renr3/HIGROTERM/Source Code/A000_SourceCode_HIGROTERM_EnPtVersion_v0_4_DUE_Version/A80_Icons.ino

/* ICONS BITMAPS
    TODO 4: Separate this icons bitmaps into an external .c file. ### Implemented on v0.4
 *  */

// int[] img_home2_png = { //:Pxs
uint16_t img_home2_png[1024] PROGMEM = { //:Wiring
  0x02FF, 0x02FF, 0x02FF, 0x02FF, 0x02FF, 0x02FF, 0x02FF, 0x02FF, 0x02FF, 0x02FF, 0x02FF, 0x02FF, 0x02FF, 0xDF3F, 0xFFDF, 0xFFDF,
  0xFFDF, 0xFFDF, 0xDF5F, 0x02FF, 0x02FF, 0x02FF, 0x02FF, 0x02FF, 0x02FF, 0x02FF, 0x02FF, 0x02FF, 0x02FF, 0x02FF, 0x02FF, 0x02FF,
  0x02FF, 0x02FF, 0x02FF, 0x02FF, 0x02FF, 0x02FF, 0x02FF, 0x02FF, 0x02FF, 0x02FF, 0x02FF, 0x02FF, 0xF7BF, 0xFFDF, 0xFFDF, 0xFFDF,
  0xFFDF, 0xFFDF, 0xFFDF, 0xF7DF, 0x02FF, 0x02FF, 0x02FF, 0xC6DF, 0xFFDF, 0xFFDF, 0x239F, 0x02FF, 0x02FF, 0x02FF, 0x02FF, 0x02FF,
  0x02FF, 0x02FF, 0x02FF, 0x02FF, 0x02FF, 0x02FF, 0x02FF, 0x02FF, 0x02FF, 0x02FF, 0x02FF, 0xEF9F, 0xFFDF, 0xFFDF, 0xFFDF, 0xFFDF,
  0xFFDF, 0xFFDF, 0xFFDF, 0xFFDF, 0xF7BF, 0x02FF, 0x02FF, 0xFFDF, 0xFFDF, 0xFFDF, 0xFFDF, 0x02FF, 0x02FF, 0x02FF, 0x02FF, 0x02FF,
  0x02FF, 0x02FF, 0x02FF, 0x02FF, 0x02FF, 0x02FF, 0x02FF, 0x02FF, 0x02FF, 0x02FF, 0xE77F, 0xFFDF, 0xFFDF, 0xFFDF, 0xFFDF, 0xFFDF,
  0xFFDF, 0xFFDF, 0xFFDF, 0xFFDF, 0xFFDF, 0xEFBF, 0x239F, 0xFFDF, 0xFFDF, 0xFFDF, 0xFFDF, 0x02FF, 0x02FF, 0x02FF, 0x02FF, 0x02FF,
  0x02FF, 0x02FF, 0x02FF, 0x02FF, 0x02FF, 0x02FF, 0x02FF, 0x02FF, 0x02FF, 0xD71F, 0xFFDF, 0xFFDF, 0xFFDF, 0xFFDF, 0xFFDF, 0xD71F,
  0xCEFF, 0xFFDF, 0xFFDF, 0xFFDF, 0xFFDF, 0xFFDF, 0xEFBF, 0xFFDF, 0xFFDF, 0xFFDF, 0xFFDF, 0x02FF, 0x02FF, 0x02FF, 0x02FF, 0x02FF,
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
0x859F,0x859F,0x859F,0x859F,0xA63F,0xF7BF,0xFFFF,0xFFFF,0xFFFF,0xFFFF,0xF7BF,0x8DBF,
0x859F,0x859F,0x859F,0x859F,0x859F,0x859F,0x859F,0x859F,0x859F,0x859F,0x859F,0x859F,
0x859F,0xA63F,0xC6DF,0xE77F,0xFFFF,0xFFFF,0xFFFF,0xFFFF,0xFFFF,0xFFFF,0xAE7F,0x859F,
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
};
// array size: 576
